Squalius-cephalus/OpenRidingController/3D_files/rev1/STEP/electronics/electronics_box_lid.step

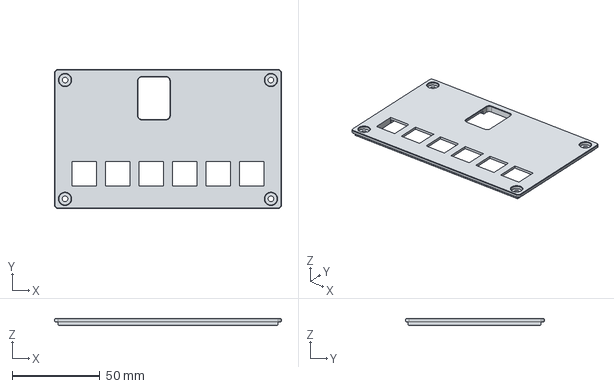
[picture p15: CAD file, 2026-05-07, an earlier design]
3D_files/rev1/STEP/electronics/electronics_box_lid.step
129.0 x 79.0 x 4.00 mm
