Squalius-cephalus/OpenRidingController/3D_files/rev1/STEP/frame/frame_connector.step

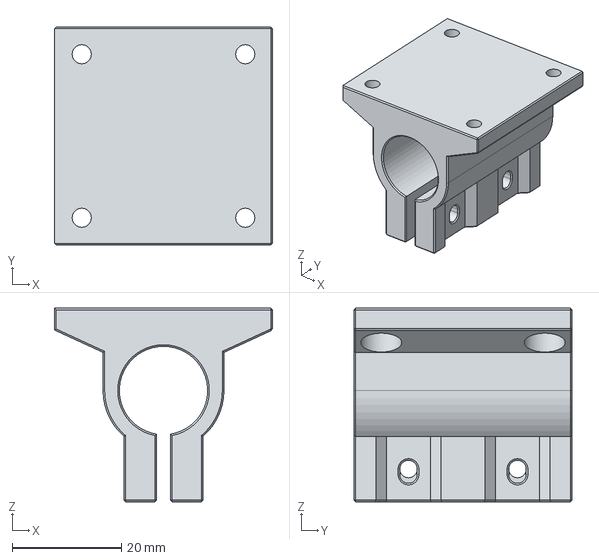
[picture p16: CAD file, 2026-04-23, an earlier design]
3D_files/rev1/STEP/frame/frame_connector.step
40.0 x 40.0 x 35.5 mm
