Squalius-cephalus/OpenRidingController/3D_files/rev1/STEP/misc/strap_adapter.step

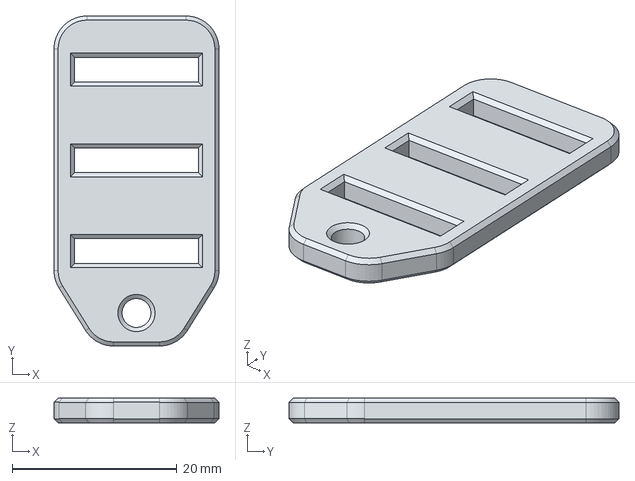
[picture p17: CAD file, 2026-05-07, an earlier design]
3D_files/rev1/STEP/misc/strap_adapter.step
20.0 x 40.0 x 3.00 mm
