Squalius-cephalus/OpenRidingController/3D_files/rev1/STEP/reins/bearing_holder.step

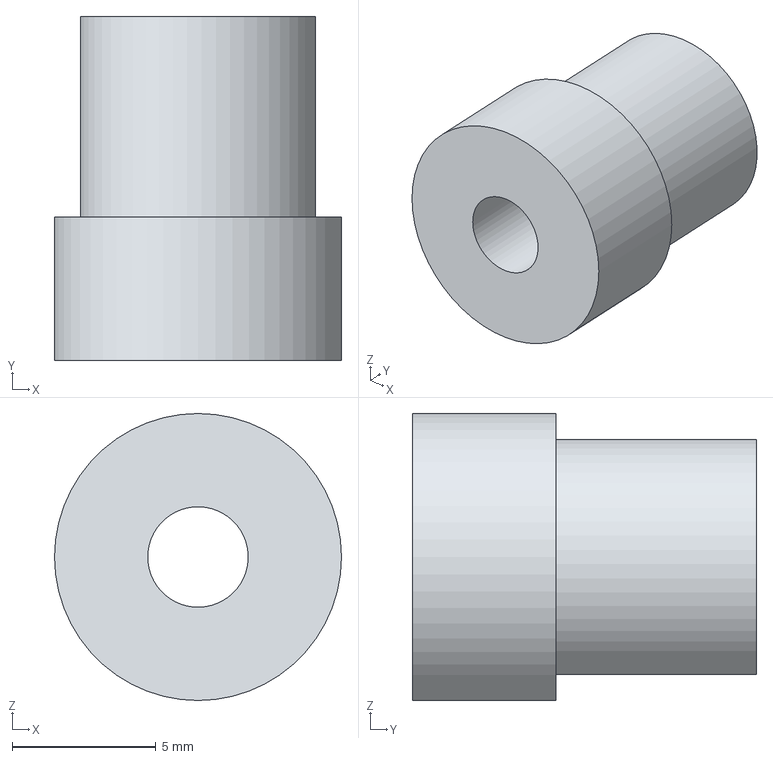
[picture p18: CAD file, 2026-05-07, an earlier design]
3D_files/rev1/STEP/reins/bearing_holder.step
10.0 x 12.0 x 10.0 mm
