Squalius-cephalus/OpenRidingController/circuitpython_code/rev2/inputs/nunchuk.py

"""
This module wraps the Adafruit Nunchuk library and provides:
- Joystick input processing
- Button state handling
- Motion flick gesture detection
- Analog state reporting
- Sensitivity and mode configuration
"""

import adafruit_nunchuk
from utils.debug import log

class NunchukHandler:
    """
    Handles all communication and input processing for a Nunchuk controller.

    This class manages:
    - I2C communication
    - Joystick analog input
    - C and Z button states
    - Flick gesture detection
    - Profile settings
    """

    def __init__(self,i2c):
        """Initialize the Nunchuk controller and internal state,
        sets connection status to false if controller is not detected
        """
        while not i2c.try_lock():
            pass

        devices = i2c.scan()
        i2c.unlock()

        if 0x52 in devices:
            log("Nunchuk detected")
            self.nunchuk_connected = True
            self.nc = adafruit_nunchuk.Nunchuk(i2c,
    i2c_read_delay=0.001)
        else:
            log("Nunchuk not detected")
            self.nunchuk_connected = False

        self.states = {}
        self.nunchuk_settings = {}
        self.nunchuk_mode = ""
        self.nunchuk_sensitivity = 0
        self.nunchuk_joystick_axis = ""

        self.nunchuk_c_released = False
        self.nunchuk_z_released = False
        self.last_time = 0
        self.last_x_nunchuk = 700
        self.last_nunchuk_flick = 0

        self.analog_x = 0
        self.analog_y = 0

        self.values = []

    def update(self, current_time):
        """
        Updates and reads joystick data, button states, and motion gestures.
        If the controller disconnects, all analog values are reset.

        Args:
            current_time: Current monotonic timestamp.
        """
        self.states = {}

        if current_time - self.last_time < 0.01:  # 100 Hz
            return

        self.last_time = current_time
        if not self.nunchuk_connected:
            return
        try:
            self.values = self.nc.values
            self.states = self.handle_nunchuk() | self.detect_flick(current_time)
            self.last_time = current_time
        except OSError:
            self.nunchuk_connected = False
            self.analog_x = 0
            self.analog_y = 0
            log("Nunchuk controller disconnected!")

    def handle_nunchuk(self):
        """
        Process joystick and button input states.

        Applies joystick centering, optional deadzone filtering,
        and adjust sensitivity based on profile setting.

        Returns:
            Dictionary containing button states.
        """

        joystick_x, joystick_y = self.values[0]
        button_c, button_z = self.values[1]

        deadzone = 5
        nunchuk_button_states = {
            "nunchuk_c_button": False,
            "nunchuk_z_button": False,
        }

        if button_c:
            nunchuk_button_states["nunchuk_c_button"] = True
        if button_z:
            nunchuk_button_states["nunchuk_z_button"] = True

        centered_x = joystick_x - 128
        centered_y = joystick_y - 128
        if self.nunchuk_mode == "mouse":
            if abs(centered_x) < deadzone:
                centered_x = 0
            if abs(centered_y) < deadzone:
                centered_y = 0

        sensitivity = self.nunchuk_sensitivity
        if sensitivity is None:
            sensitivity = 1
        centered_x = int(centered_x * sensitivity)
        centered_y = int(centered_y * sensitivity)

        self.analog_x = centered_x
        self.analog_y = centered_y

        return nunchuk_button_states

    def detect_flick(self, current_time):
        """
        Detect rapid left or right flick gestures using accelerometer data.

        A flick is detected when acceleration change exceeds a
        configured threshold and enough time has passed since
        the previous flick.

        Args:
            current_time: Current monotonic timestamp.

        Returns:
            Dictionary containing flick states.
        """
        nunchuk_flick_states = {
            "nunchuk_flick_left": False,
            "nunchuk_flick_right": False,
        }

        x, y, z = self.values[2]

        flick_threshold = 450

        accel_x = x - self.last_x_nunchuk

        if (current_time - self.last_nunchuk_flick) > 0.2:
            if abs(accel_x) > flick_threshold:
                if accel_x > 0:
                    nunchuk_flick_states["nunchuk_flick_right"] = True
                    log(accel_x)
                else:
                    nunchuk_flick_states["nunchuk_flick_left"] = True
                    log(accel_x)
                self.last_nunchuk_flick = current_time

        self.last_x_nunchuk = x

        return nunchuk_flick_states

    def set_new_profile(self, profile):
        """
        Sets joystick sensitivity, mode and 
        what joystick needs to be controlled based on the profile.
        """
        self.nunchuk_settings = profile["nunchuk_mode"]
        self.nunchuk_mode = self.nunchuk_settings.get("mode")
        self.nunchuk_sensitivity = self.nunchuk_settings.get("sensitivity")
        self.nunchuk_joystick_axis = self.nunchuk_settings.get("axis")

    def get_states(self):
        """
        Returns:
            Dictionary containing button and flick states.
        """
        return self.states

    def is_connected(self):
        """
        Returns:
            Status if controller connected.
        """
        return self.nunchuk_connected

    def get_analog_states(self):
        """
        Combines all analog states.

        Returns:
            Dictionary containing analog joystick state data,
            if controller is detected.
        """
        if not self.nunchuk_connected:
            return None
        return {
            "x": self.analog_x,
            "y": self.analog_y,
            "mode": self.nunchuk_mode,
            "sensitivity": self.nunchuk_sensitivity,
            "axis": self.nunchuk_joystick_axis,
        }
